oskitone/higher_lower/arduino/higher_lower/graphics.h

// clang-format off

const unsigned char PROGMEM machine[] =
{
// width, height,
62, 62,
// FRAME 00
0xc0, 0x30, 0x08, 0x04, 0x02, 0x02, 0x01, 0x21, 0x21, 0x01, 0x81, 0x01, 0x21, 0x61, 0xe1, 0x41, 0x01, 0x01, 0x21, 0x21, 0x61, 0x01, 0x01, 0x01, 0x21, 0x61, 0xe1, 0xc1, 0x81, 0x01, 0x21, 0x61, 0xe1, 0xc1, 0x81, 0x01, 0x01, 0x81, 0x41, 0x21, 0xa1, 0xa1, 0xa1, 0xa1, 0xa1, 0xa1, 0xa1, 0xa1, 0xa1, 0xa1, 0xa1, 0xa1, 0xa1, 0xa1, 0x21, 0x41, 0x82, 0x02, 0x04, 0x08, 0x30, 0xc0, 
0xff, 0x00, 0x00, 0x00, 0x00, 0xc7, 0x8c, 0x1c, 0x18, 0x40, 0xe3, 0xc3, 0x0c, 0x1c, 0x08, 0x61, 0xe3, 0xc7, 0x86, 0x10, 0x30, 0x71, 0xe3, 0xc7, 0x8e, 0x0c, 0x18, 0x71, 0xe3, 0xc7, 0x8e, 0x1c, 0x38, 0x71, 0xe3, 0x00, 0x00, 0xff, 0x00, 0xff, 0x00, 0x00, 0x00, 0x80, 0xc0, 0x30, 0x18, 0x18, 0x30, 0xc0, 0x80, 0x00, 0x00, 0x00, 0xff, 0x00, 0xff, 0x00, 0x00, 0x00, 0x00, 0xff, 
0xff, 0x00, 0x00, 0x00, 0x00, 0x71, 0xe3, 0x80, 0x0e, 0x1c, 0x38, 0x00, 0x22, 0xc7, 0x8e, 0x1c, 0x38, 0x71, 0xe3, 0xc7, 0x8e, 0x1c, 0x38, 0x71, 0xe3, 0xc7, 0x8e, 0x1c, 0x00, 0x71, 0xe3, 0x06, 0x80, 0x1c, 0x38, 0x00, 0x00, 0xff, 0x00, 0xff, 0x08, 0x08, 0x08, 0xc9, 0xc9, 0x49, 0x49, 0x49, 0x49, 0xc9, 0xc9, 0x08, 0x08, 0x08, 0xff, 0x00, 0xff, 0x00, 0x00, 0x00, 0x00, 0xff, 
0xff, 0x00, 0x00, 0x00, 0x00, 0x1c, 0x38, 0x71, 0xe0, 0xc1, 0x86, 0x0c, 0x18, 0x30, 0xa1, 0x43, 0x06, 0x14, 0x30, 0x61, 0x63, 0x47, 0x06, 0x14, 0x38, 0x31, 0x80, 0xc6, 0x8e, 0x14, 0x38, 0x70, 0xe3, 0xc7, 0x8e, 0x00, 0x00, 0xff, 0x00, 0x7f, 0x80, 0x80, 0x80, 0x80, 0x81, 0x86, 0x8c, 0x8c, 0x86, 0x81, 0x80, 0x80, 0x80, 0x80, 0x7f, 0x00, 0xff, 0x00, 0x00, 0x00, 0x00, 0xff, 
0xff, 0x00, 0x00, 0x00, 0x00, 0xc0, 0xe0, 0x60, 0x60, 0x61, 0xe3, 0xc3, 0x02, 0xc0, 0xe0, 0x61, 0x63, 0x43, 0x02, 0xe0, 0xe0, 0x81, 0xc3, 0xe3, 0x62, 0x00, 0xe0, 0xe1, 0x03, 0x63, 0x62, 0xe0, 0xe0, 0x61, 0x60, 0xc0, 0xe0, 0x60, 0x61, 0x62, 0xe2, 0xc2, 0x02, 0xe2, 0xe2, 0xe2, 0x82, 0x02, 0x02, 0xe2, 0xe2, 0x02, 0xe2, 0xe2, 0x62, 0x61, 0x60, 0x00, 0x00, 0x00, 0x00, 0xff, 
0xff, 0x00, 0x00, 0x00, 0x00, 0x0f, 0x1f, 0x18, 0x18, 0x18, 0x1f, 0x0f, 0x00, 0x19, 0x1b, 0x1f, 0x1e, 0x0e, 0x00, 0x1f, 0x1f, 0x07, 0x0f, 0x1c, 0x18, 0x00, 0x1f, 0x1f, 0x00, 0x00, 0x00, 0x1f, 0x1f, 0x00, 0x00, 0x0f, 0x1f, 0x18, 0x18, 0x18, 0x1f, 0x0f, 0x00, 0x1f, 0x1f, 0x01, 0x07, 0x0f, 0x1c, 0x1f, 0x1f, 0x00, 0x1f, 0x1f, 0x1b, 0x1b, 0x1b, 0x00, 0x00, 0x00, 0x00, 0xff, 
0xff, 0x00, 0x00, 0x00, 0x00, 0xfe, 0xff, 0x83, 0xef, 0x83, 0xff, 0x83, 0xff, 0xc7, 0xbb, 0xbb, 0x8b, 0xff, 0x83, 0xef, 0xef, 0x83, 0xff, 0x83, 0xab, 0xab, 0xff, 0x83, 0xeb, 0xcb, 0xb7, 0xff, 0xff, 0x83, 0xbf, 0xbf, 0xff, 0x83, 0xbb, 0x83, 0xff, 0xe3, 0x8f, 0xe3, 0x8f, 0xe3, 0xff, 0x83, 0xab, 0xab, 0xff, 0x83, 0xeb, 0xcb, 0xb7, 0xff, 0xfe, 0x00, 0x00, 0x00, 0x00, 0xff, 
0x00, 0x03, 0x04, 0x08, 0x10, 0x10, 0x21, 0x21, 0x21, 0x21, 0x21, 0x21, 0x21, 0x21, 0x21, 0x21, 0x21, 0x21, 0x21, 0x21, 0x21, 0x21, 0x21, 0x21, 0x21, 0x21, 0x21, 0x21, 0x21, 0x21, 0x21, 0x21, 0x21, 0x21, 0x21, 0x21, 0x21, 0x21, 0x21, 0x21, 0x21, 0x21, 0x21, 0x21, 0x21, 0x21, 0x21, 0x21, 0x21, 0x21, 0x21, 0x21, 0x21, 0x21, 0x21, 0x21, 0x10, 0x10, 0x08, 0x04, 0x03, 0x00,
};

const unsigned char PROGMEM sound[] =
{
// width, height,
9, 29,
// FRAME 00
0x00, 0x00, 0x00, 0x40, 0x80, 0x80, 0x80, 0x01, 0x02, 
0x40, 0x40, 0x40, 0x40, 0x40, 0x40, 0x40, 0x01, 0x00, 
0x00, 0x00, 0x00, 0x40, 0x20, 0x20, 0x20, 0x10, 0x00, 
0x00, 0x00, 0x00, 0x00, 0x00, 0x00, 0x10, 0x08, 0x00,
};
